higemaru/kewbie/kewbie36tp_lili/other_items/bottom.png

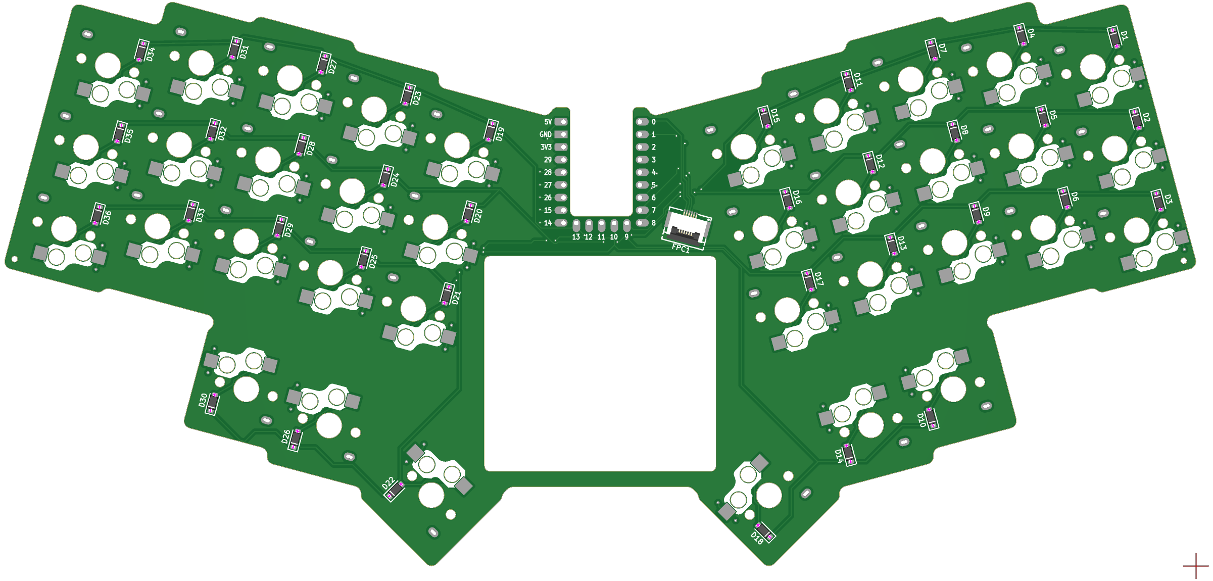
kewbie36tp_lili/other_items/bottom.png
