higemaru/kewbie/kewbie36tp_lili/other_items/top.png

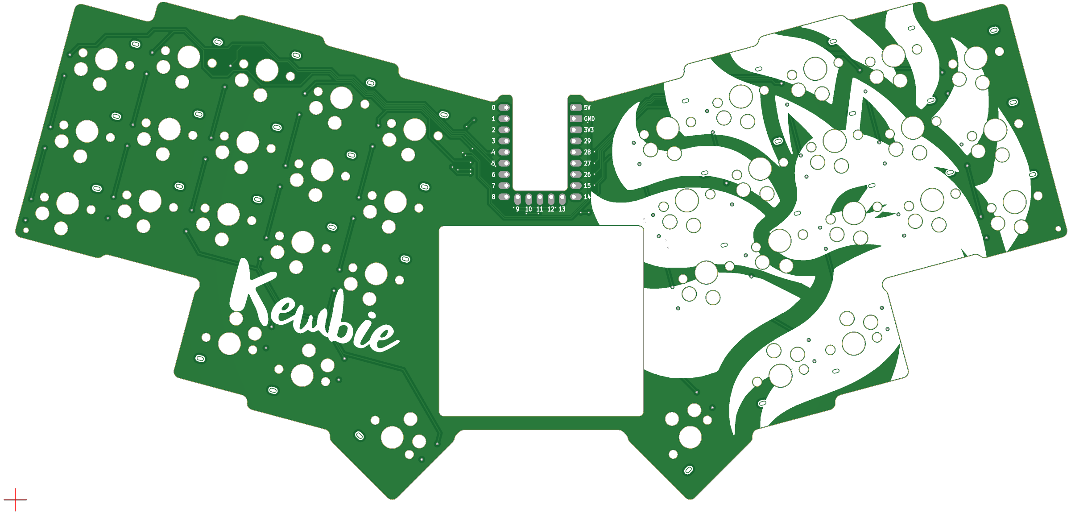
kewbie36tp_lili/other_items/top.png
