higemaru/kewbie/kewbie46/guide/images/MCU_solder_06.png

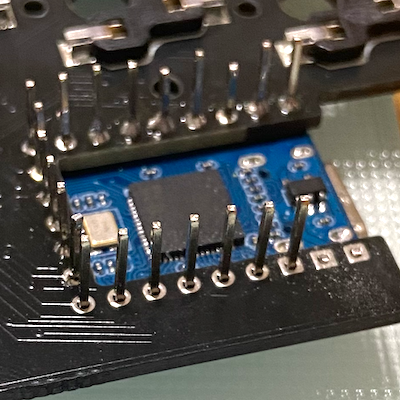
kewbie46/guide/images/MCU_solder_06.png
